juraspb/Musical-LEDS/strip/1.png

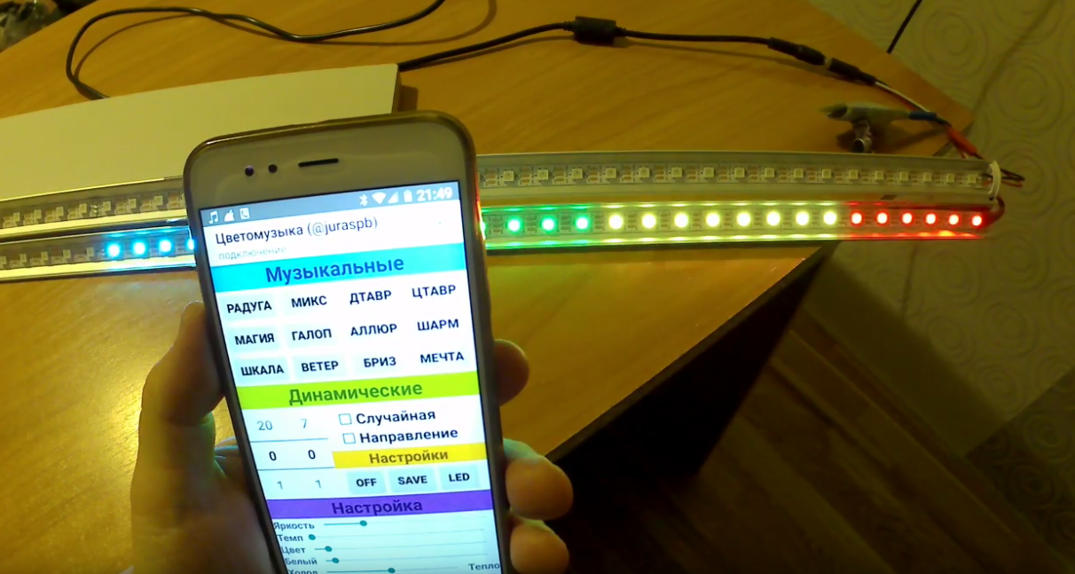
strip/1.png
