juraspb/Musical-LEDS/strip/2.png

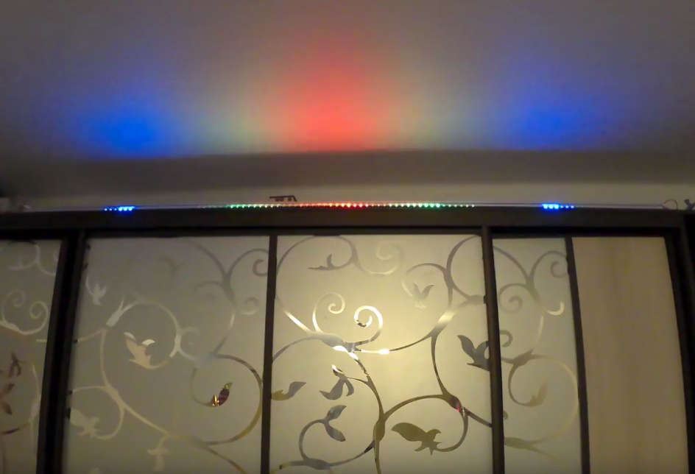
strip/2.png
