juraspb/Musical-LEDS/strip/3.png

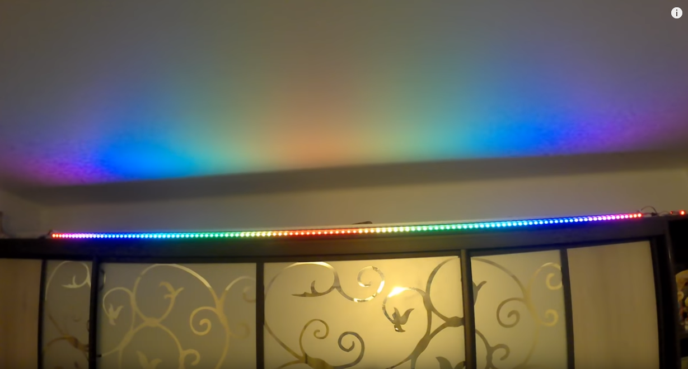
strip/3.png
