juraspb/Musical-LEDS/strip/5.png

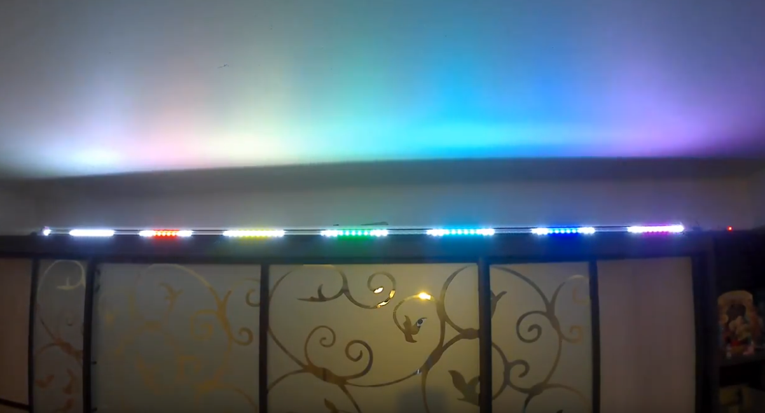
strip/5.png
