juraspb/Musical-LEDS/strip/6.png

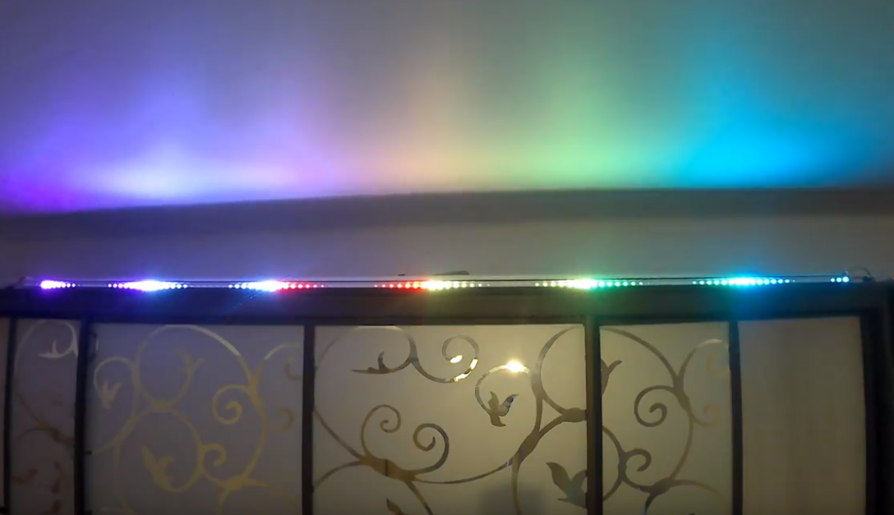
strip/6.png
